FutureSharks/preamp-two/prototypes/prototype-16.jpg

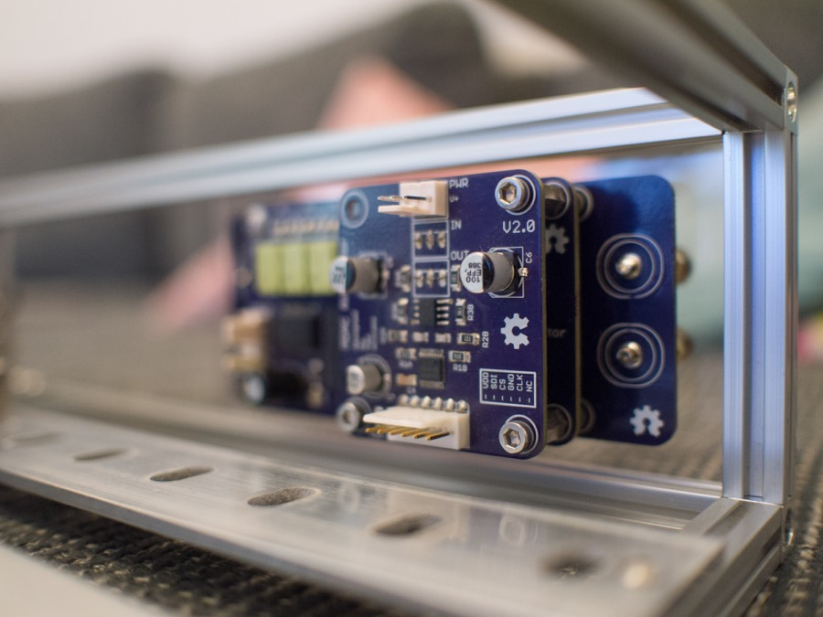
prototypes/prototype-16.jpg
