FutureSharks/preamp-two/measurements/20190811_161510.jpg

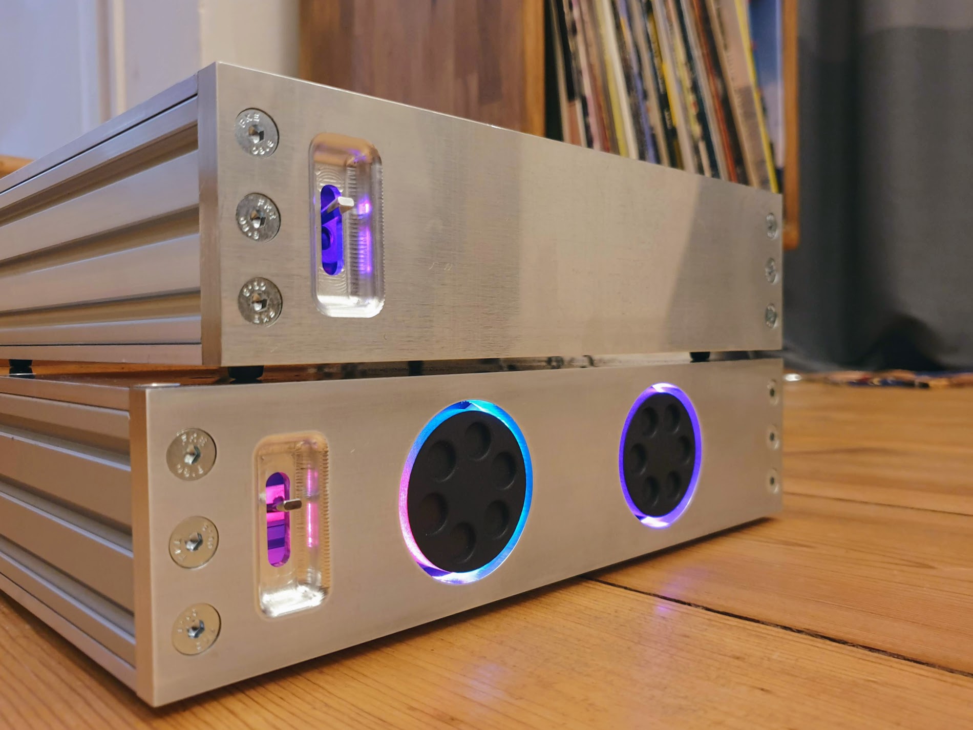
measurements/20190811_161510.jpg
